wirbel-at-vdr-portal/GPS_XCXO/Ltspice/filter_comparison.asc

C1: cap; 10µ
C2: cap; 10µ
C3: cap; 10µ
C4: cap; 10µ
C5: cap; 10µ
C6: cap; 10µ
C7: cap; 100µ
R1: res; 1k
R2: res; 1k
R3: res; 100k
R4: res; 1k
R5: res; 1k
R6: res; 10k
R7: res; 10k
R8: res; 100k
R9: res; 10k
R10: res; 100k
V1: voltage; PULSE(0 5 1n 1n 1n 0.5m 1m); AC 1
Named nets: 0, out1, out2, out3, out4, out5, out6
;tran 5
.ic V(out1)=2.21
;op
.ac dec 10 0.1 100k
